vannaka/Heated_Bed_Controller/src/heater/temp_table.h

#ifndef TEMPTABLE
#define TEMPTABLE

const short temp_table[][2] =
 {
    { 1 * 4,    938 }, 
    { 31 * 4,   314 },
    { 41 * 4,   290 },
    { 51 * 4,   272 },
    { 61 * 4,   258 }, 
    { 71 * 4,   247 }, 
    { 81 * 4,   237 }, 
    { 91 * 4,   229 }, 
    { 101 * 4,  221 }, 
    { 111 * 4,  215 }, 
    { 121 * 4,  209 },
    { 131 * 4,  204 }, 
    { 141 * 4,  199 }, 
    { 151 * 4,  195 }, 
    { 161 * 4,  190 }, 
    { 171 * 4,  187 }, 
    { 181 * 4,  183 }, 
    { 191 * 4,  179 }, 
    { 201 * 4,  176 }, 
    { 221 * 4,  170 }, 
    { 241 * 4,  165 },
    { 261 * 4,  160 }, 
    { 281 * 4,  155 }, 
    { 301 * 4,  150 }, 
    { 331 * 4,  144 }, 
    { 361 * 4,  139 }, 
    { 391 * 4,  133 }, 
    { 421 * 4,  128 }, 
    { 451 * 4,  123 }, 
    { 491 * 4,  117 }, 
    { 531 * 4,  111 },
    { 571 * 4,  105 }, 
    { 611 * 4,  100 }, 
    { 681 * 4,  90  }, 
    { 711 * 4,  85  }, 
    { 811 * 4,  69  }, 
    { 831 * 4,  65  },
    { 881 * 4,  55  },
    { 901 * 4,  51  },  
    { 941 * 4,  39  }, 
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
};

#endif // TEMPTABLE
